MagnusPer/Balboa-GS510SZ/examples/Balboa_GS_HomeAssistant/Balboa_GS_HomeAssistant.ino

  /*
 *    
 *    Main board: Wemos D1 mini - esp8266
 *  
 *    SPA display controller for Balboa system GS510SZ 
 *    
 */
    

#include <WiFiClient.h>
#ifdef ESP32
#include <WebServer.h>
#include <WiFi.h>
#else
#include <ESP8266WebServer.h>
#include <ESP8266WiFi.h>  
#endif
#include <ElegantOTA.h>                  // https://github.com/ayushsharma82/ElegantOTA
#include <ArduinoHA.h>
#include <Balboa_GS_Interface.h>        // https://github.com/MagnusPer/Balboa-GS510SZ    

#ifdef ESP32
#define setClockPin 1 // CHANGE ME
#define setReadPin  1 // CHANGE ME
#define setWritePin 1 // CHANGE ME 
#else
#define setClockPin D1  
#define setReadPin  D2 
#define setWritePin D8  
#endif

//Constants
const char *wifi_ssid                    = "";          // WiFi SSID
const char *wifi_pwd                     = "";          // WiFi Password 
const char *wifi_hostname                = "SPA";
const char* mqtt_server                  = "";           // MQTT Boker IP, your home MQTT server eg Mosquitto on RPi, or some public MQTT
const int mqtt_port                      = 1883;        // MQTT Broker PORT, default is 1883 but can be anything.
const char *mqtt_user                    = "";          // MQTT Broker User Name
const char *mqtt_pwd                     = "";          // MQTT Broker Password 

//Globals 
bool debug                               = true;    // If true activate debug values to write to serial port

const unsigned long ReportTimerMillis    = 30000;   // Timer in milliseconds to report mqtt topics 
unsigned long ReportTimerPrevMillis      = 0;       // Store previous millis

byte mac[] = {0x00, 0x10, 0xFA, 0x6E, 0x32, 0x4A};  // Leave this value, unless you own multiple hot tubs


// MQTT Constants
const char* mqtt_Subscribe_write_topic      = "SPA/Write"; 
const char* mqtt_Subscribe_updateTemp_topic = "SPA/UpdateTemp";

//Initialize components
WiFiClient espClient;                                           // Setup WiFi client definition WiFi
HADevice device(mac, sizeof(mac));
HAMqtt mqtt(espClient, device, 30);
BalboaInterface Balboa(setClockPin, setReadPin, setWritePin);   // Setup Balboa interface 
#ifdef ESP32
WebServer server(80);
#else
ESP8266WebServer server(80);
#endif

HASensor display("Display");
HASensorNumber waterTemp("waterTemp", HANumber::PrecisionP1);
HABinarySensor heater("Heater");
HABinarySensor pump1("Pump1");
HABinarySensor pump2("Pump2");
HABinarySensor pump3("Pump3");
HABinarySensor lights("Lights");
HAButton pump1Button("Pump1");
HAButton pump2Button("Pump2");
HAButton pump3Button("Pump3");
HAButton lightsButton("Lights");
HAButton tempUpButton("TempUp");
HAButton tempDownButton("TempDown");
HAButton modeButton("Mode");

HAHVAC hvac(
  "temp",
  HAHVAC::TargetTemperatureFeature
);

void onTargetTemperatureCommand(HANumeric temperature, HAHVAC* sender) {
    float temperatureFloat = temperature.toFloat();

    Serial.print("Target temperature: ");
    Serial.println(temperatureFloat);

    Balboa.updateTemperature(temperatureFloat);

    sender->setTargetTemperature(temperature); // report target temperature back to the HA panel
}

 
/**************************************************************************/
/* Setup                                                                  */
/**************************************************************************/

void setup() {
  
  if (debug) { Serial.begin(115200); Serial.println("Welcome to SPA - Balboa system GS510SZ");}
  setup_wifi();
  setup_HA();
  Serial.begin(115200);
  Balboa.begin();

  server.on("/", []() {
    server.send(200, "text/plain", "Hi! I am ESP8266.");
  });
  
  ElegantOTA.begin(&server);    // Start ElegantOTA
  server.begin();
  if (debug) { Serial.println("HTTP server started"); }

}


/**************************************************************************/
/* Setup WiFi connection                                                  */
/**************************************************************************/

void setup_wifi() {

    /*  WiFi status return values and meaning 
        WL_IDLE_STATUS      = 0,
        WL_NO_SSID_AVAIL    = 1,
        WL_SCAN_COMPLETED   = 2,
        WL_CONNECTED        = 3,
        WL_CONNECT_FAILED   = 4,
        WL_CONNECTION_LOST  = 5,
        WL_WRONG_PASSWORD   = 6,
        WL_DISCONNECTED     = 7 */
  
    if (debug){ Serial.print("WiFi.status(): "); Serial.println(WiFi.status()); }
    
    int WiFi_retry_counter = 0;
    WiFi.mode(WIFI_STA);
    WiFi.hostname(wifi_hostname);
    #ifdef ESP32
    WiFi.setSleep(false);
    #else
    WiFi.setSleepMode(WIFI_NONE_SLEEP);
    #endif
    WiFi.begin(wifi_ssid, wifi_pwd);
    
    // Loop until reconnected or max retry then restart
    while (WiFi.status() != WL_CONNECTED){
        WiFi_retry_counter ++;
        if (WiFi_retry_counter == 30) {ESP.restart();}  
        if (debug){ Serial.print("WiFi.status(): "); Serial.print(WiFi.status()); 
                    Serial.print("   WiFi retry: "); Serial.println(WiFi_retry_counter); } 
        delay(1000);
    }
    
    if (debug){ Serial.print("WiFi connected: ");Serial.println(WiFi.localIP());}

}


void setup_HA() {
    device.setName("Hottub");
    device.setSoftwareVersion("1.2");
    device.setManufacturer("Balboa");
    device.setModel("GS510SZ");

    waterTemp.setUnitOfMeasurement("°C");
    waterTemp.setDeviceClass("temperature");
    waterTemp.setName("Water temperature");

    display.setName("Display");
    heater.setName("Heater");

    pump1.setName("Pump1");
    pump1Button.setName("Pump1");
    pump1Button.onCommand(onButtonPress);

    pump2.setName("Pump2");
    pump2Button.setName("Pump2");
    pump2Button.onCommand(onButtonPress);

    pump3.setName("Pump3");
    pump3Button.setName("Pump3");
    pump3Button.onCommand(onButtonPress);

    lights.setName("Lights");
    lightsButton.setName("Lights");
    lightsButton.onCommand(onButtonPress);


    tempUpButton.setName("Temp Up");
    tempUpButton.onCommand(onButtonPress);

    tempDownButton.setName("Temp Down");
    tempDownButton.onCommand(onButtonPress);

    modeButton.setName("Mode");
    modeButton.onCommand(onButtonPress);


    // configure HVAC (optional)
    hvac.setName("Temp");
    hvac.setMinTemp(20);
    hvac.setMaxTemp(40);
    hvac.setTempStep(0.5);

    mqtt.begin(mqtt_server, mqtt_user, mqtt_pwd);

}

/**************************************************************************/
/* Main loop                                                              */
/**************************************************************************/

void loop() {

	Balboa.loop();
  mqtt.loop();
  server.handleClient();
  
  if (WiFi.status() != WL_CONNECTED){ setup_wifi(); }             // Check WiFi connnection reconnect otherwise 
 
    if(millis() - ReportTimerPrevMillis  > ReportTimerMillis) {
    
          ReportTimerPrevMillis = millis();
          
          display.setValue(Balboa.LCD_display.c_str());
          waterTemp.setValue(Balboa.waterTemperature);
          heater.setState(Balboa.displayHeater);
          pump1.setState(Balboa.displayPump1);
          pump2.setState(Balboa.displayPump2);
          // pump3.setState(Balboa.displayPump3);
          lights.setState(Balboa.displayLight);
          hvac.setCurrentTargetTemperature(Balboa.waterTemperature);
    } 
     
}

/**************************************************************************/
/* Subscribe to MQTT topic                                                */
/**************************************************************************/

void onButtonPress(HAButton* sender) {
  
    // Handling incoming messages

    Serial.println(sender->getName());

    String s_payload = sender->getName();
         
             if (s_payload == "TempUp") {
                  Balboa.writeDisplayData = true; 
                  Balboa.writeTempUp      = true;
             }
             else if (s_payload == "TempDown") {
                  Balboa.writeDisplayData = true;
                  Balboa.writeTempDown    = true;  
             }
             else if (s_payload == "Light") {
                  Balboa.writeDisplayData = true;
                  Balboa.writeLight       = true; 
             }
             else if (s_payload == "Pump1") {
                  Balboa.writeDisplayData = true;
                  Balboa.writePump1       = true;  
             }
             else if (s_payload == "Pump2") {
                  Balboa.writeDisplayData = true;
                  Balboa.writePump2       = true;  
             }
             else if (s_payload == "Pump3") {
                  Balboa.writeDisplayData = true;
                  Balboa.writePump3       = true;  
             }
             else if (s_payload == "Mode") {
                  Balboa.writeDisplayData = true;
                  Balboa.writeMode        = true;  
             }
             else if (s_payload == "Stop") {
                  Balboa.stop();
             }
             else if (s_payload == "Reset") {
                ESP.restart();
             }
      
}
      
